sparkfun/SparkFun_GNSS_mosaic-X5/docs/assets/img/README.md

img directory
====================
This folder should contain the images for the product documentation

## General Images
* `sfe_logo_sm.png` - SparkFun flame logo (Cover page for with-pdf extension)
* `sfe_logo_sq.png` - SparkFun flame logo (favicon)

## Directory
* `hookup_guide` - Images for the hookup guide pages

## QR Codes
* [QR code generator](https://qrgenerator.org/)
	* Flame Color: #E0311D
	* Frame Color: #3C464D
	* Label Font: Arial
* [Remove meta data from svg](https://jakearchibald.github.io/svgomg/)
