sparkfun/SparkFun_GNSS_mosaic-X5/docs/background.md

---
icon: material/bookshelf
---

Below, are several articles, application notes, and other technical resources:

* Manufacturer Resources
	* [GPS / GNSS correction services](https://www.septentrio.com/en/products/gps/gnss-correction-services)
		* [Getting the most out of correction services with an agnostic receiver](https://www.septentrio.com/en/learn-more/insights/getting-most-out-correction-services-agnostic-receiver)
		* Land
			* [Agnostic Corrections Program - GNSS correction services compatible with Septentrio receivers](https://www.septentrio.com/en/products/correction-services/precise-point-positioning-services-land/agnostic-corrections-program-gnss-correction-services)
		* [GNSS corrections for Japan](https://www.septentrio.com/en/company/corrections-services-land/clas)
		* Sea
			* [Marinestar - Precise Point Positioning (PPP) Correction Services](https://www.septentrio.com/en/products/gps/gnss-correction-services/correction-services-marine/marinestar)
		* Timing
			* [Fugro AtomiChron™ - global, real-time, precise clock synchronization and authentication service](https://www.septentrio.com/en/products/gps/gnss-correction-services/correction-services-timing/atomichron)
	* [AIM+ anti-jamming and anti-spoofing protection](https://www.septentrio.com/en/learn-more/advanced-positioning-technology/aim-resilient-and-secure-gnss/gps-receivers)
	* Webinars
		* [GNSS Corrections Demystified](https://www.septentrio.com/en/learn-more/webinars/webinar-gnss-corrections-demystified)

	* [NGS: User Guidelines for Single Base Real Time GNSS Positioning](https://www.ngs.noaa.gov/PUBS_LIB/NGSRealTimeUserGuidelines.v2.1.pdf)
	* [International Association of Geodesy: Sub-Commission 4.5 - Next Generation RTK](http://www.wasoft.de/e/iagwg451/)

[ROS Driver](https://wiki.ros.org/septentrio_gnss_driver)

* [NTRIP](https://github.com/goblimey/go-ntrip)
