sparkfun/SparkFun_GNSS_mosaic-X5/docs/assets/img/hookup_guide/assembly-breadboard-radio-jumper.jpg

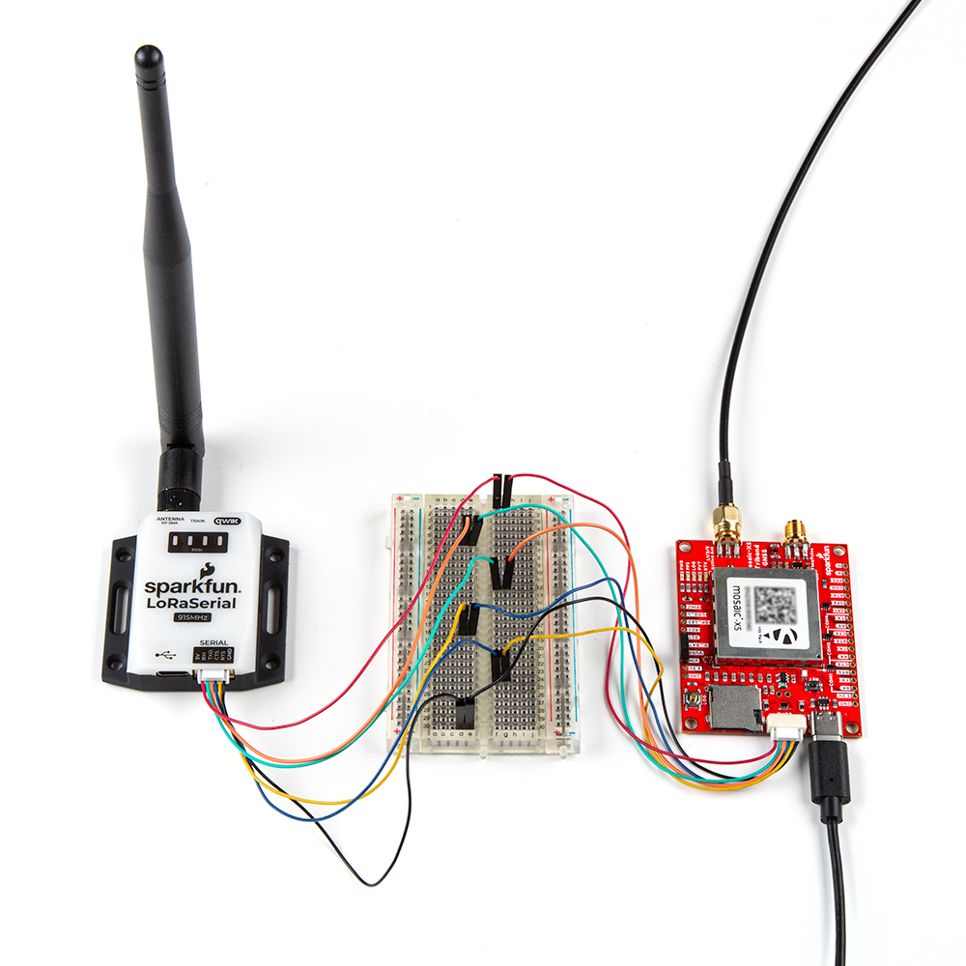
docs/assets/img/hookup_guide/assembly-breadboard-radio-jumper.jpg
