sparkfun/SparkFun_GNSS_mosaic-X5/docs/assets/img/hookup_guide/assembly-jst-radio-jumper.jpg

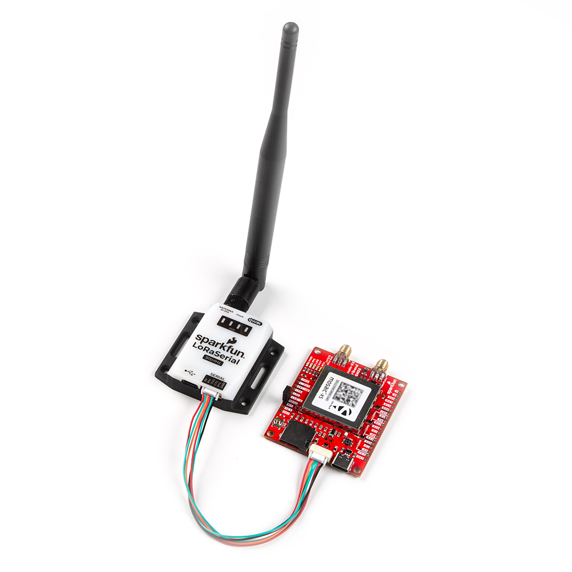
docs/assets/img/hookup_guide/assembly-jst-radio-jumper.jpg
