sparkfun/SparkFun_GNSS_mosaic-X5/docs/assets/img/hookup_guide/assembly-jst-radio_setup-jumper.jpg

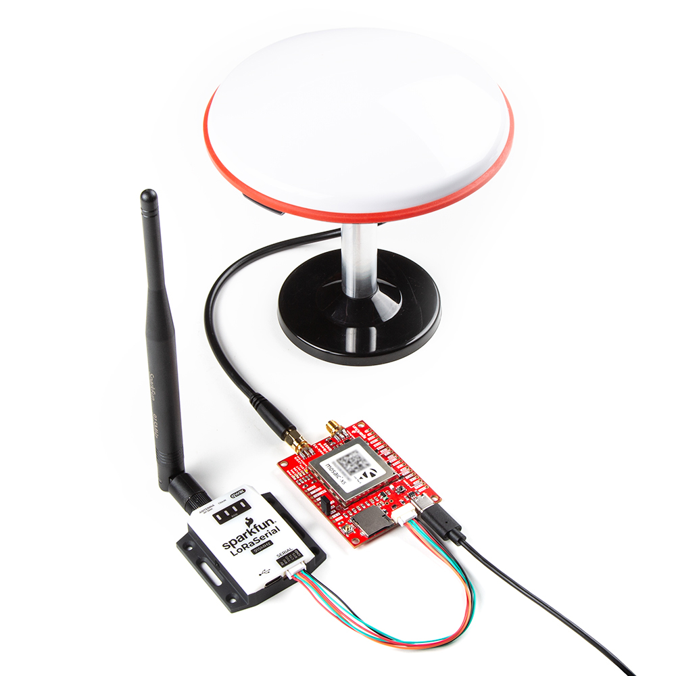
docs/assets/img/hookup_guide/assembly-jst-radio_setup-jumper.jpg
