sparkfun/SparkFun_GNSS_mosaic-X5/docs/assets/img/hookup_guide/buttons-reset2.jpg

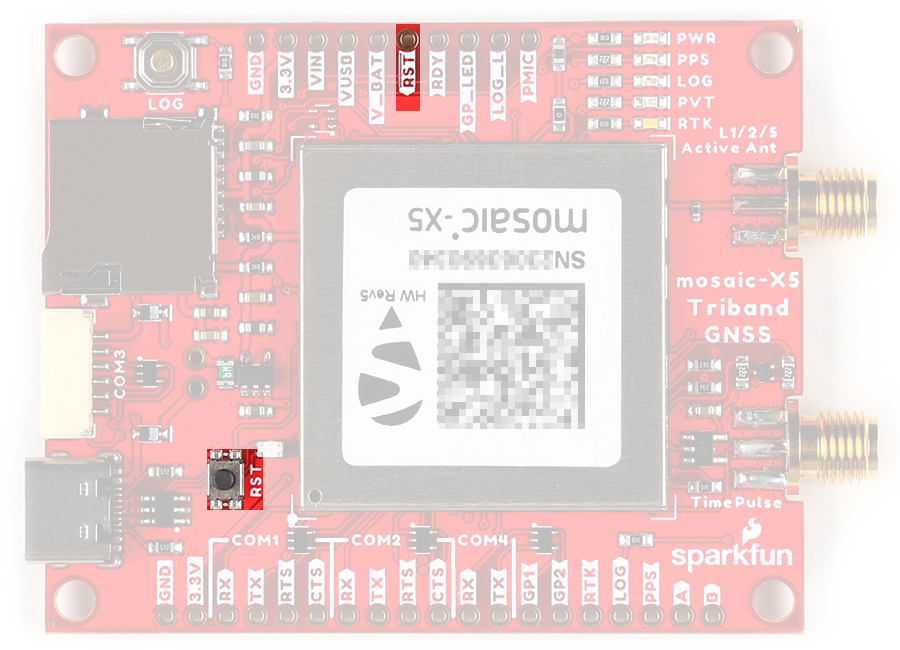
docs/assets/img/hookup_guide/buttons-reset2.jpg
