sparkfun/SparkFun_GNSS_mosaic-X5/docs/assets/img/hookup_guide/LED_connections.jpg

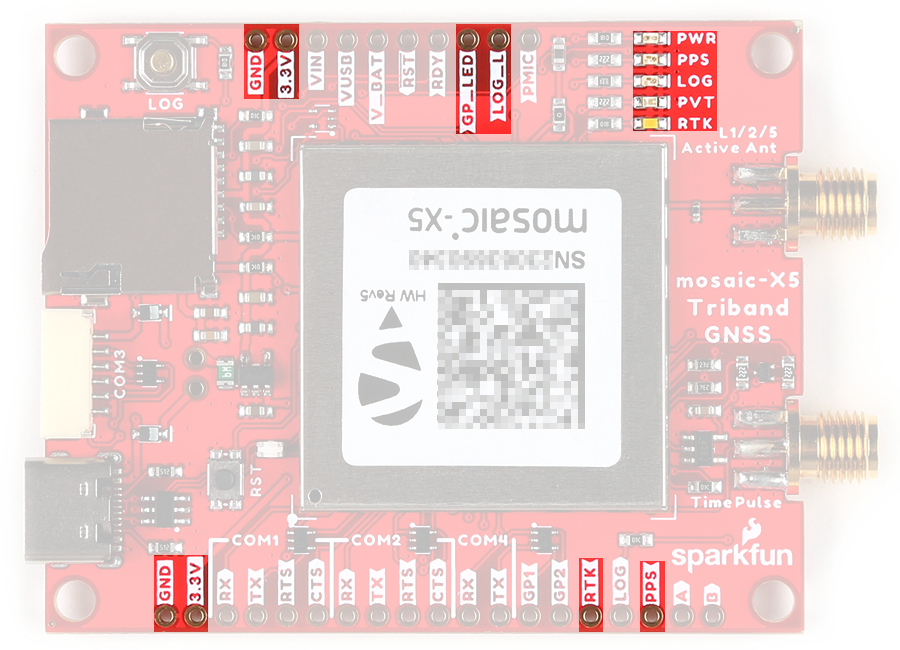
docs/assets/img/hookup_guide/LED_connections.jpg
