sparkfun/SparkFun_GNSS_mosaic-X5/docs/assets/board_files/dimensions.pdf

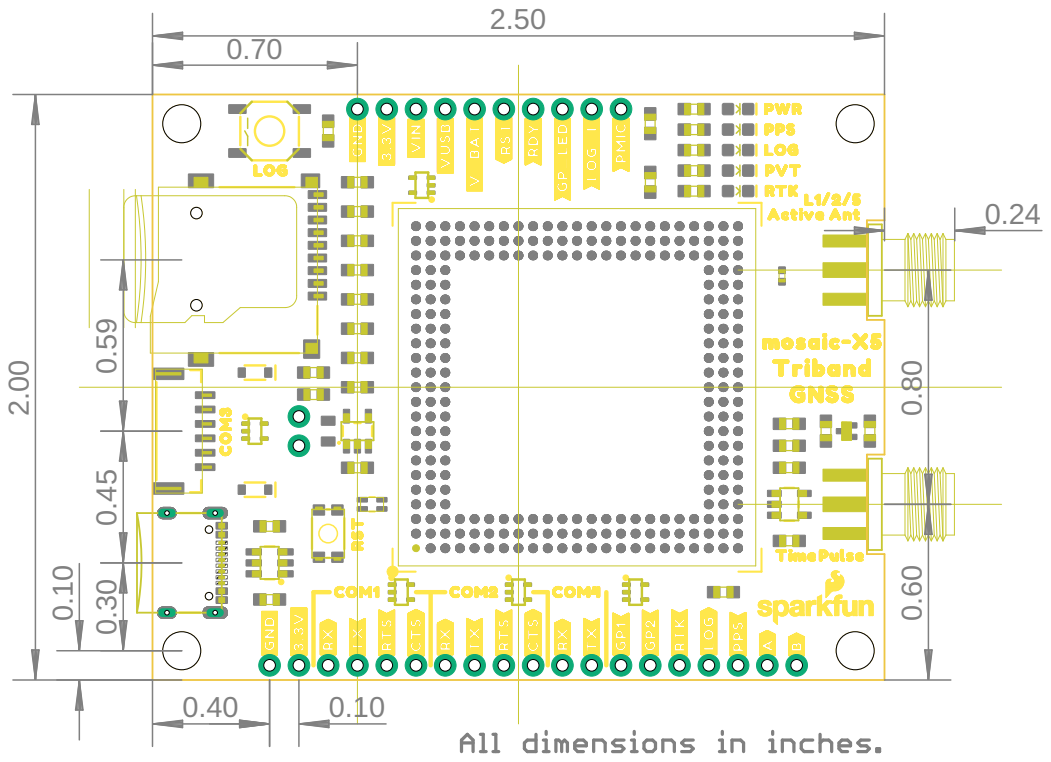
[picture p68: page 1]
